pstimpel/ConstantLoad/media/title_16_9.jpg

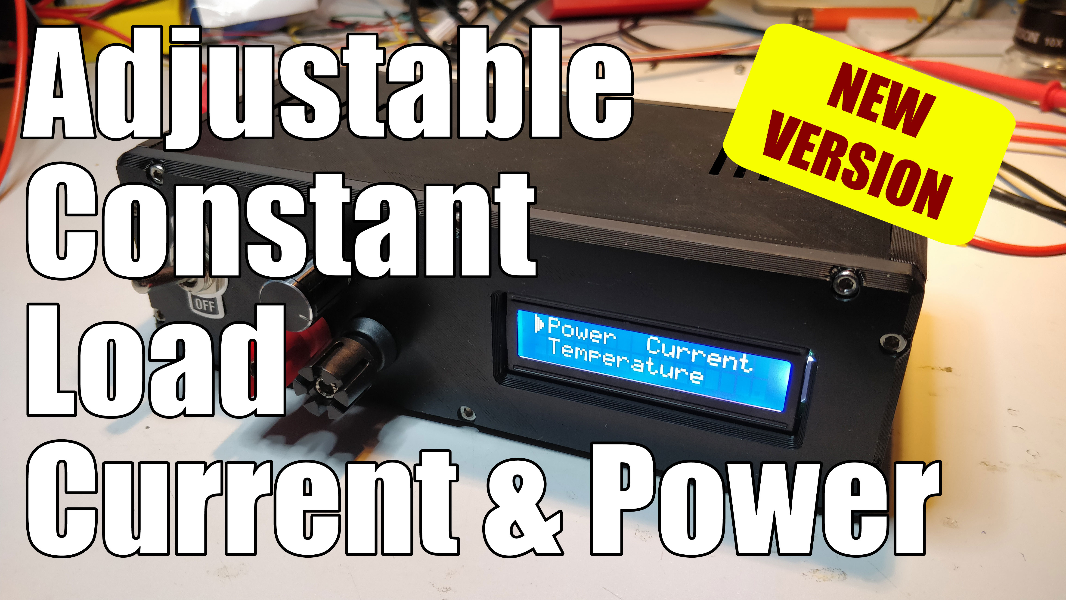
media/title_16_9.jpg
